proboterror/ZX_BUS_Mouse/images/deltagon_1.5_mouse_controller.png

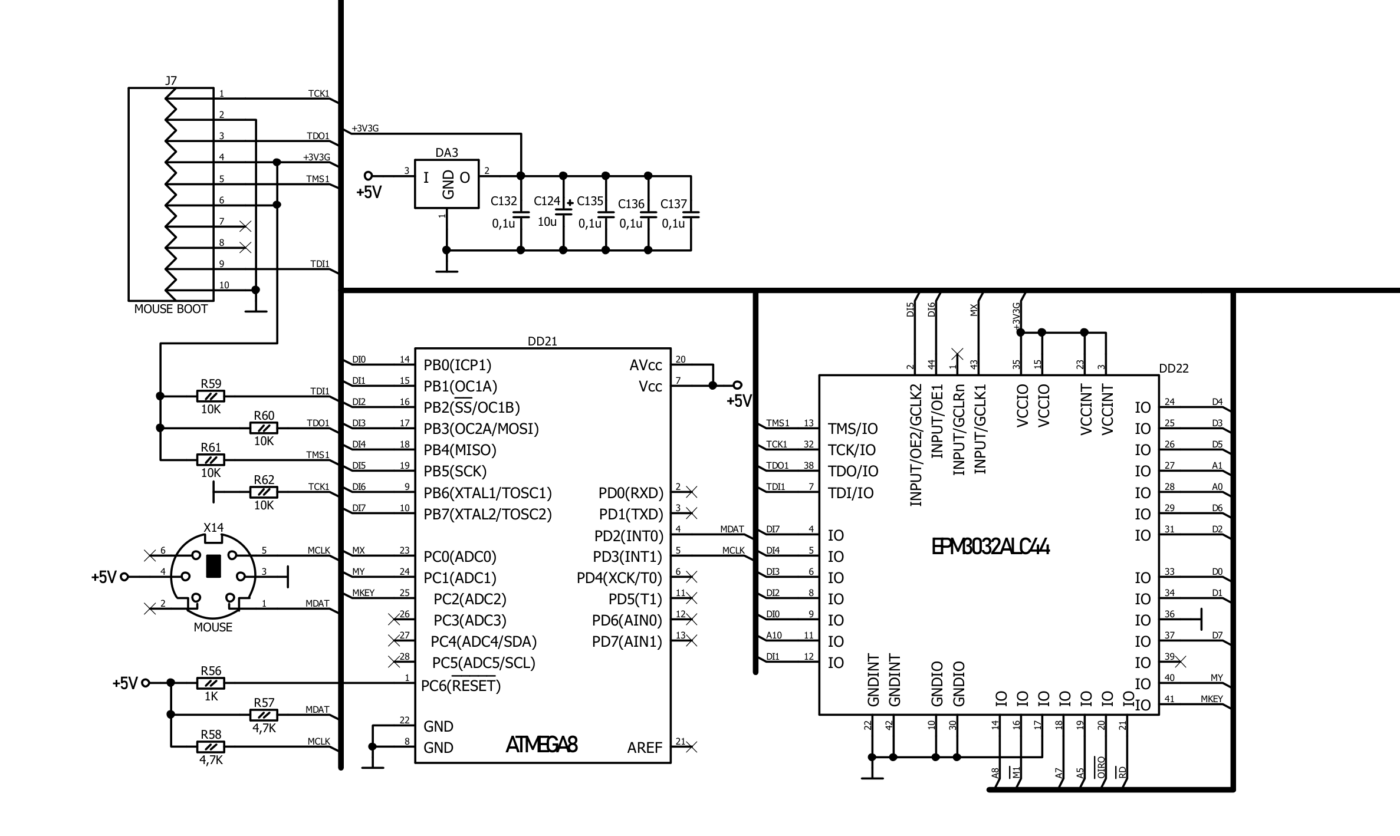
images/deltagon_1.5_mouse_controller.png
