proboterror/ZX_BUS_Mouse/source/ATmega/fuses.png

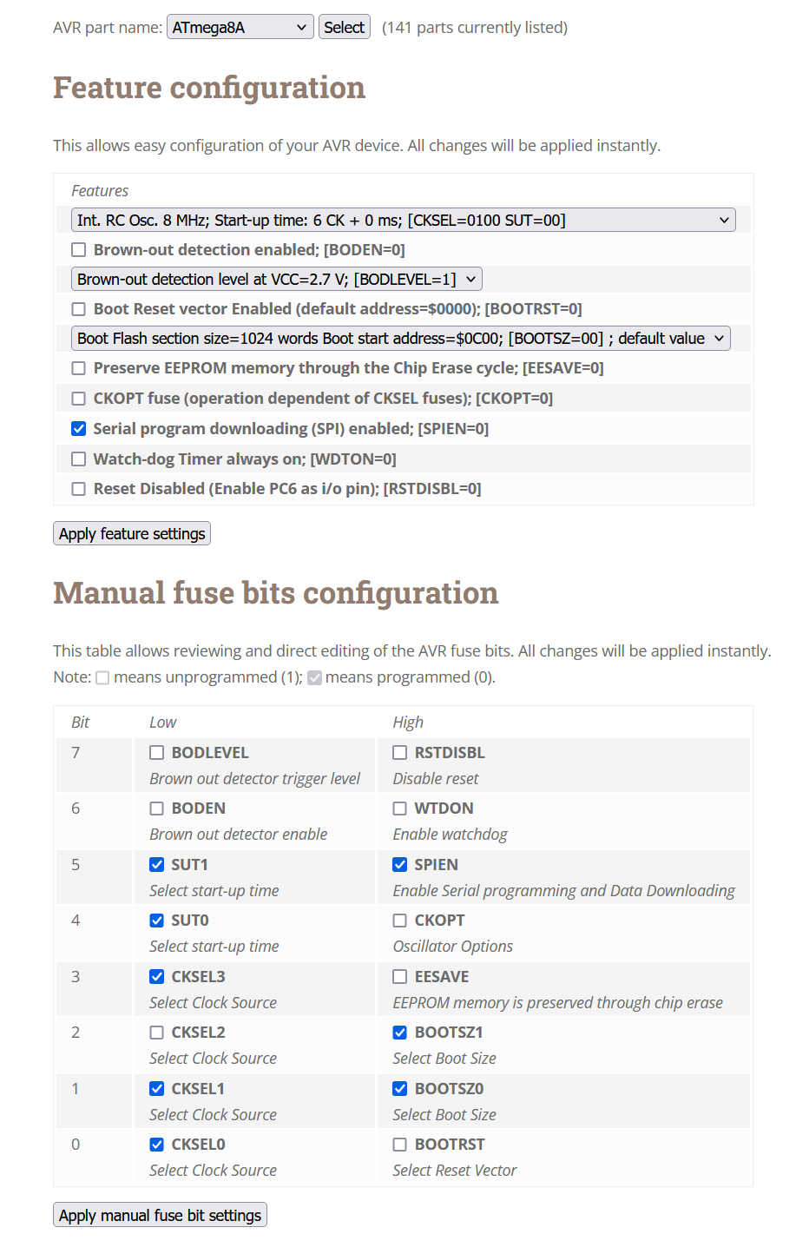
source/ATmega/fuses.png
