proboterror/ZX_BUS_Mouse/history/dejavu_0a.png

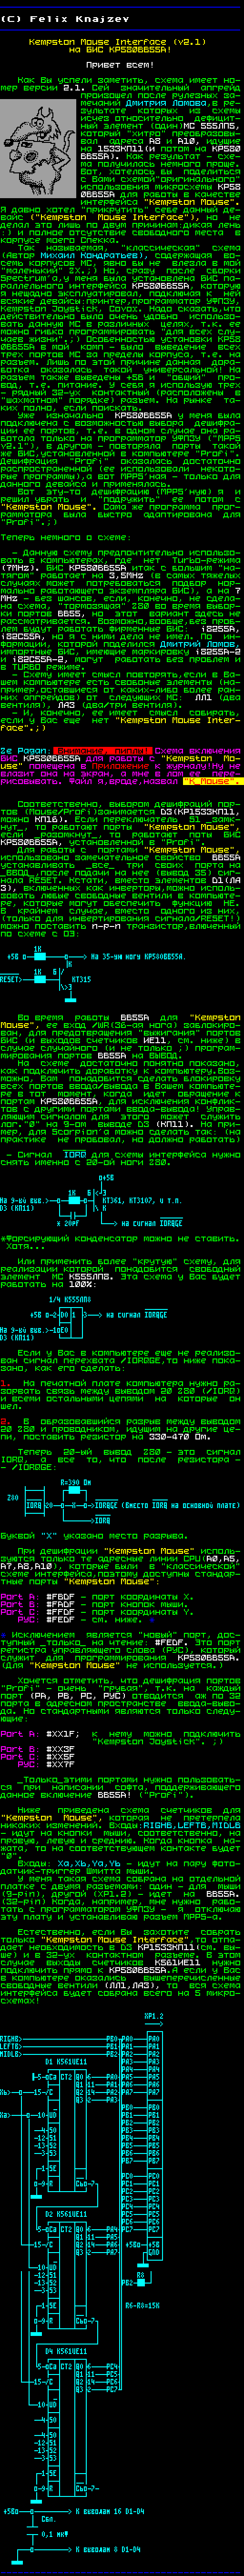
history/dejavu_0a.png
