proboterror/ZX_BUS_Mouse/history/donnews_19.png

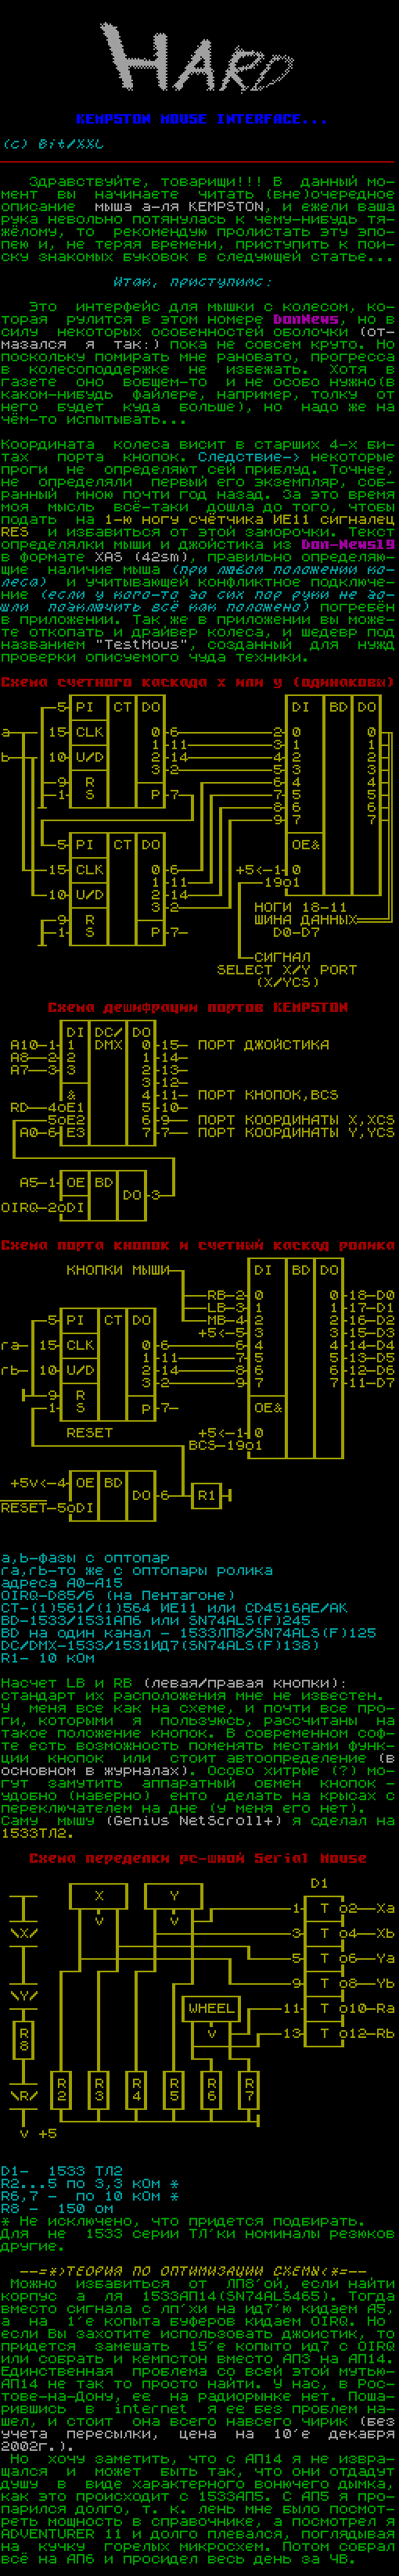
history/donnews_19.png
