proboterror/ZX_BUS_Mouse/history/scorpion_keyboard_mouse_controller_2.1_1.png

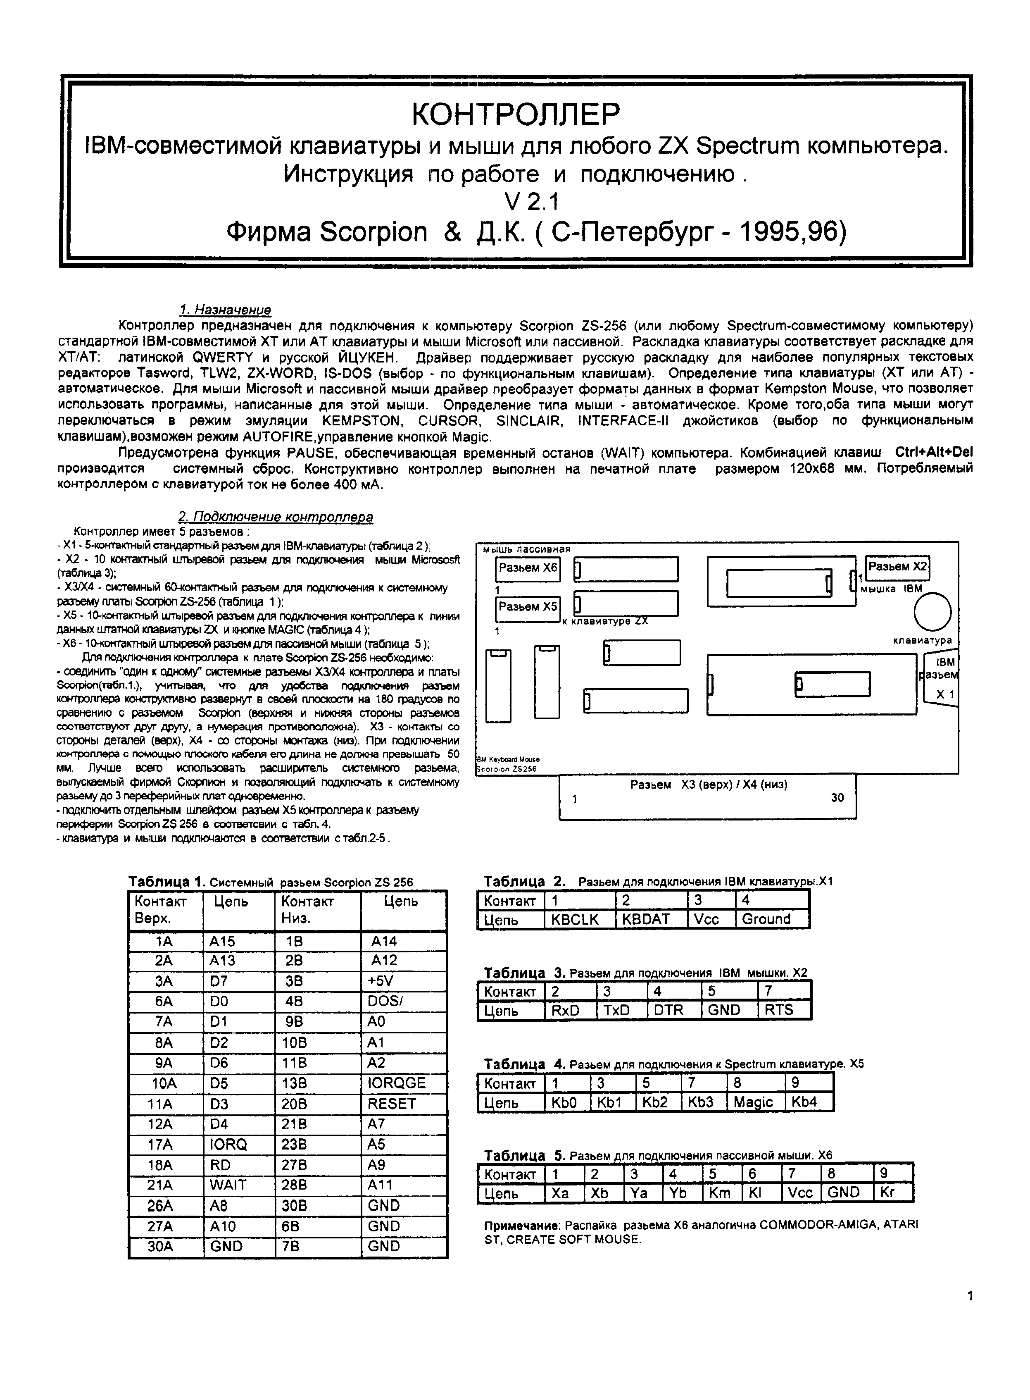
history/scorpion_keyboard_mouse_controller_2.1_1.png
