proboterror/ZX_BUS_Mouse/history/scorpion_keyboard_mouse_controller_2.1_2.png

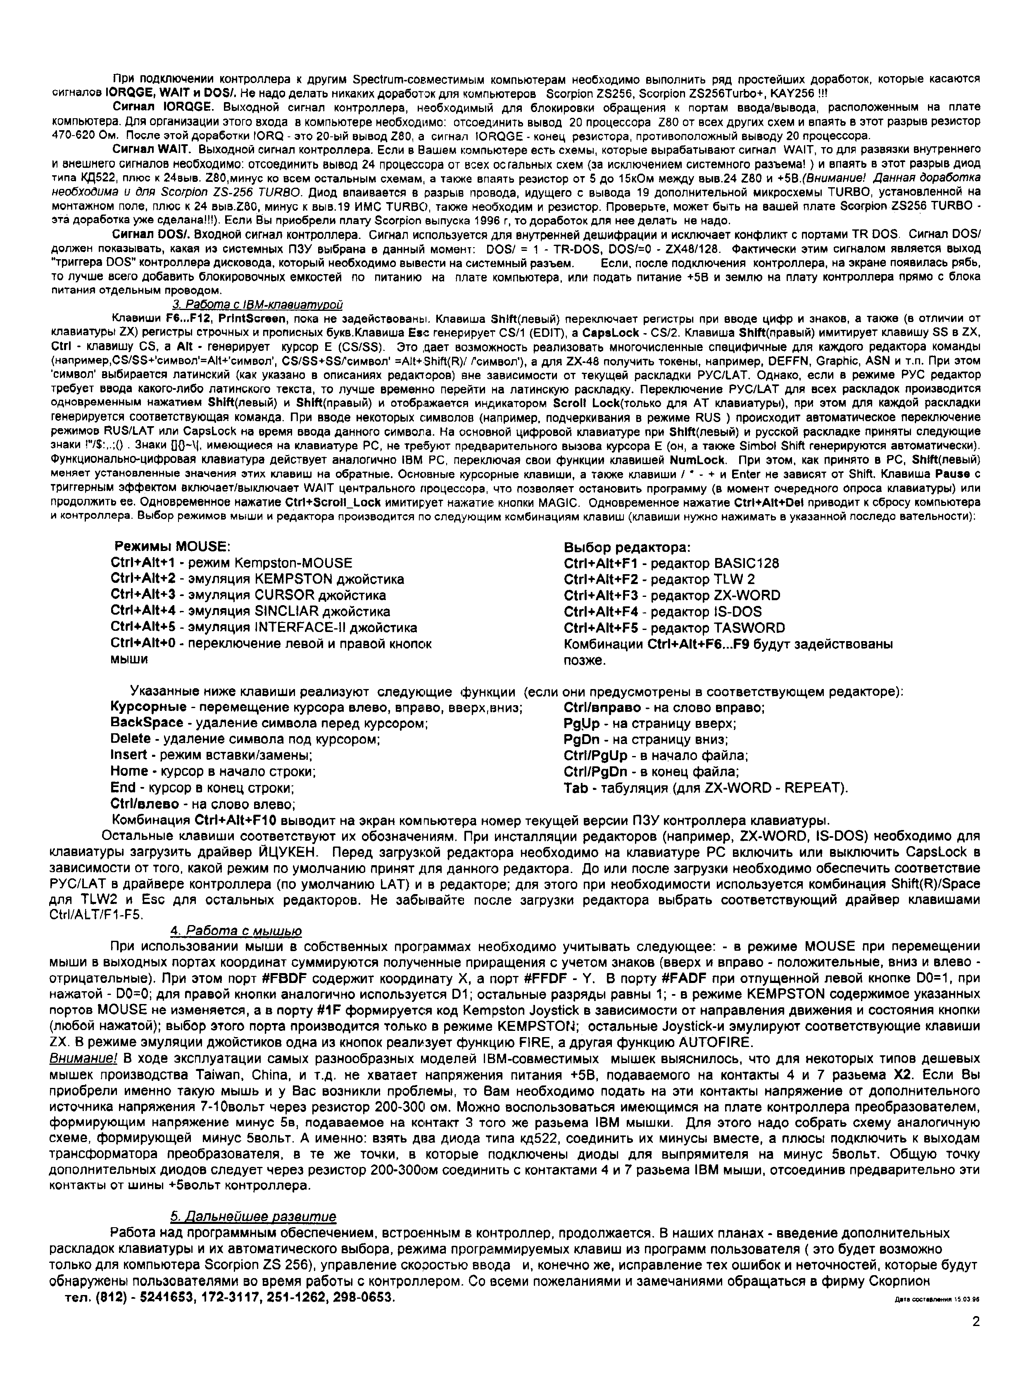
history/scorpion_keyboard_mouse_controller_2.1_2.png
