proboterror/ZX_BUS_Mouse/history/scorpion_keyboard_mouse_controller_2.5_1.jpg

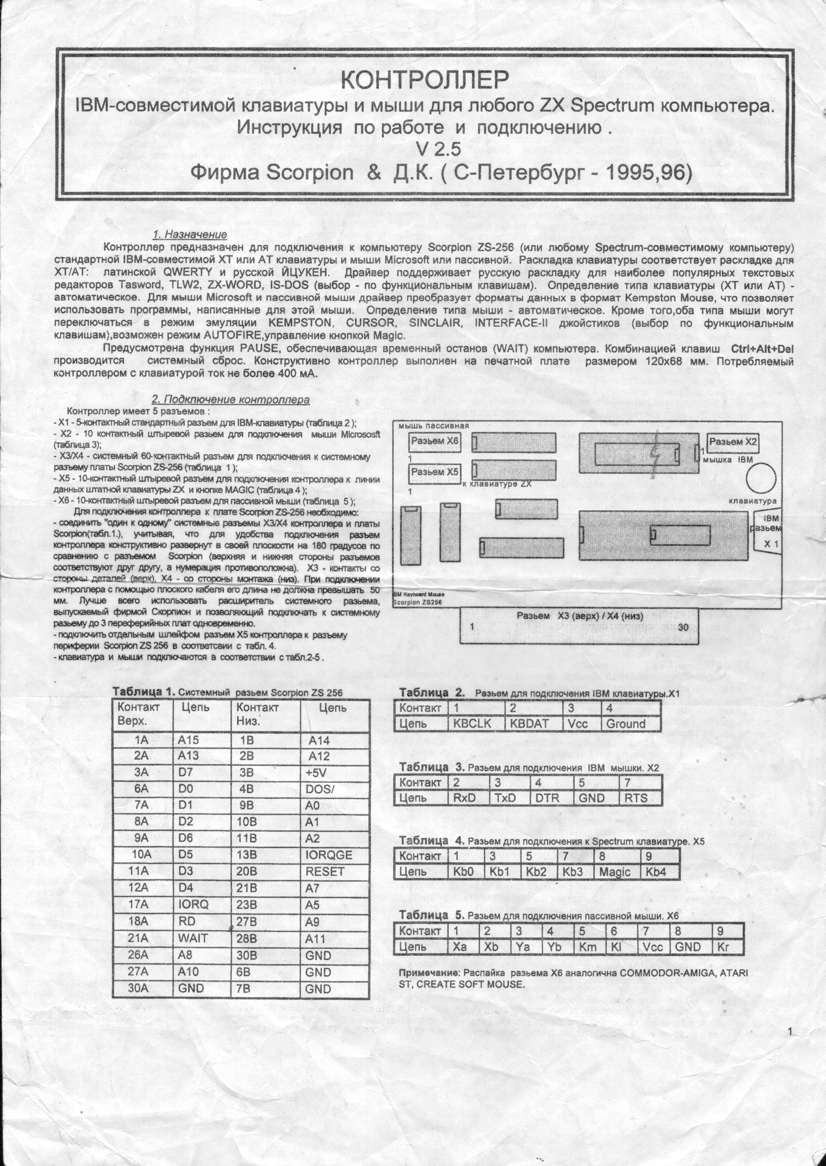
history/scorpion_keyboard_mouse_controller_2.5_1.jpg
