proboterror/ZX_BUS_Mouse/history/scorpion_keyboard_mouse_controller_scheme.png

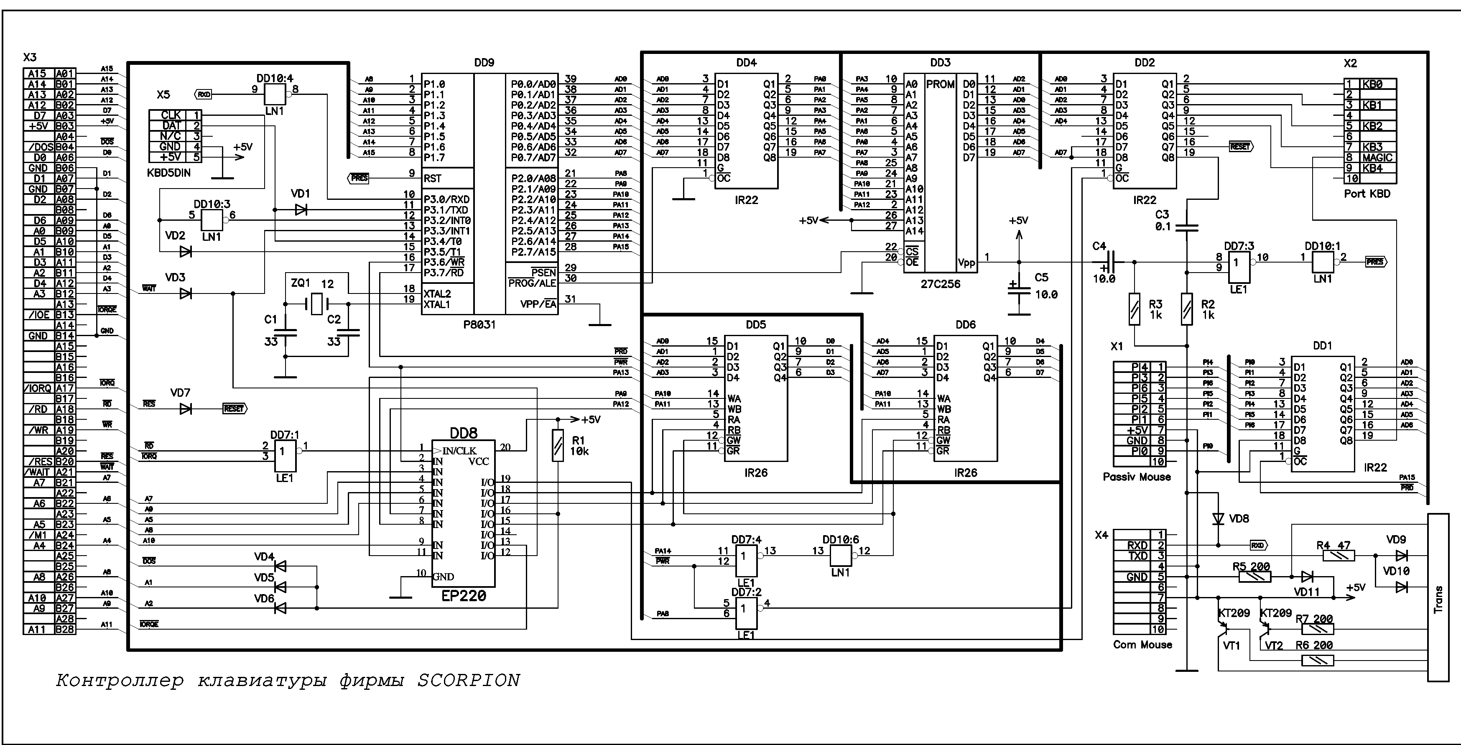
history/scorpion_keyboard_mouse_controller_scheme.png
