proboterror/ZX_BUS_Mouse/history/zx-review_1995-01.png

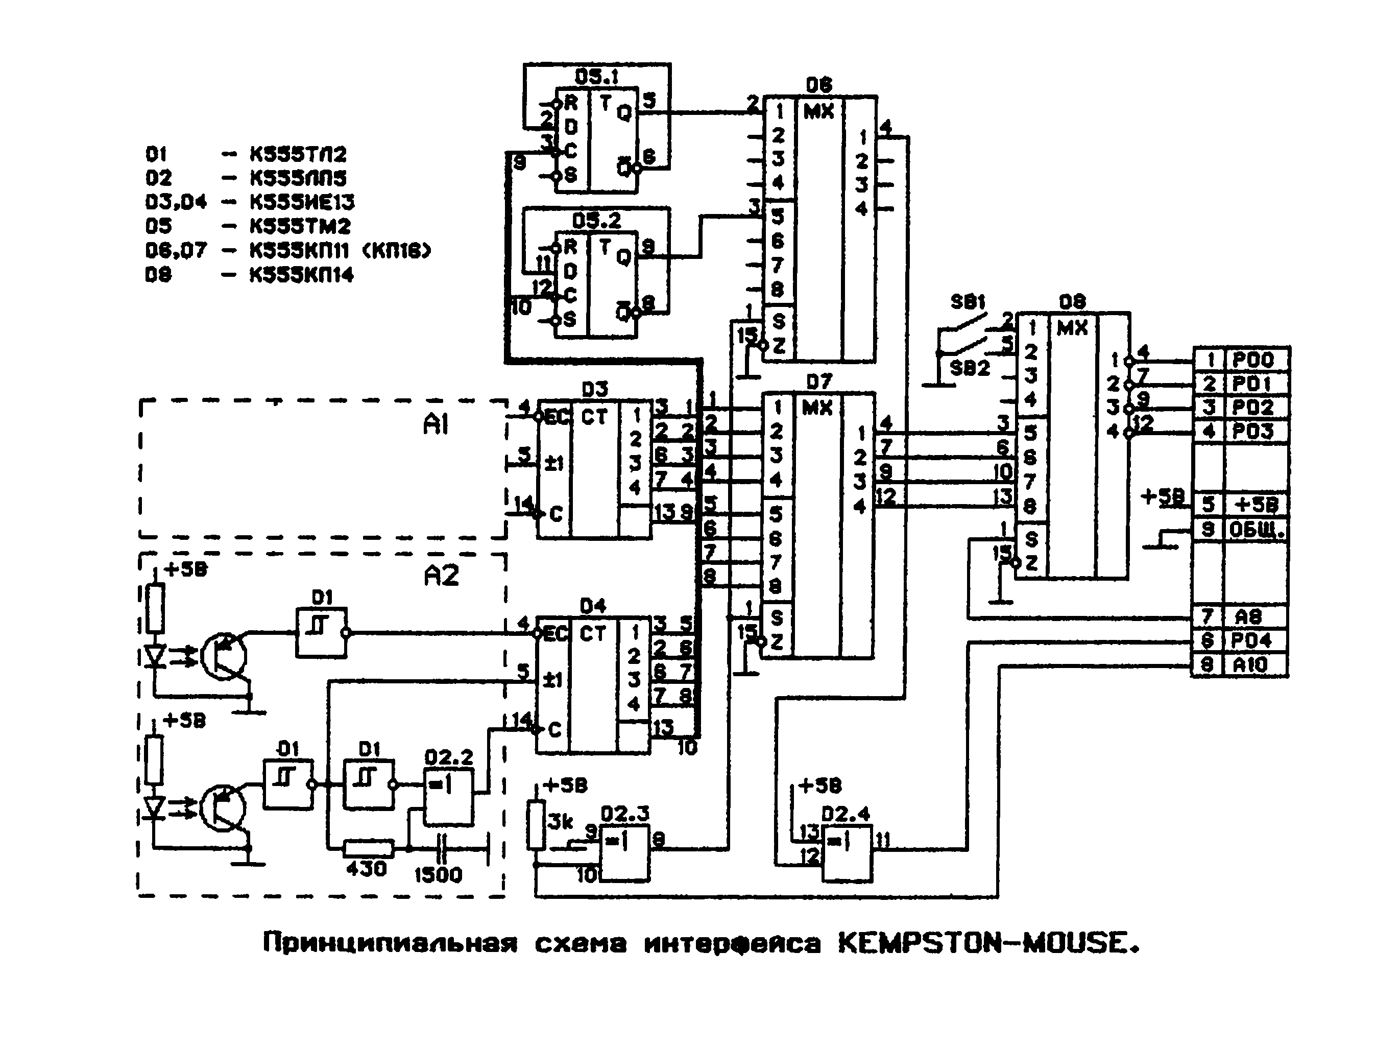
history/zx-review_1995-01.png
